bryanduxbury/roominator/photos/2012-01-26_09-58-38_41.jpg

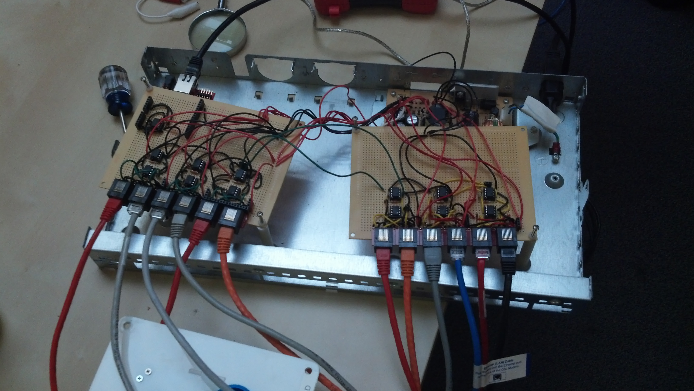
photos/2012-01-26_09-58-38_41.jpg
