bryanduxbury/roominator/photos/2012-01-26_09-58-45_927.jpg

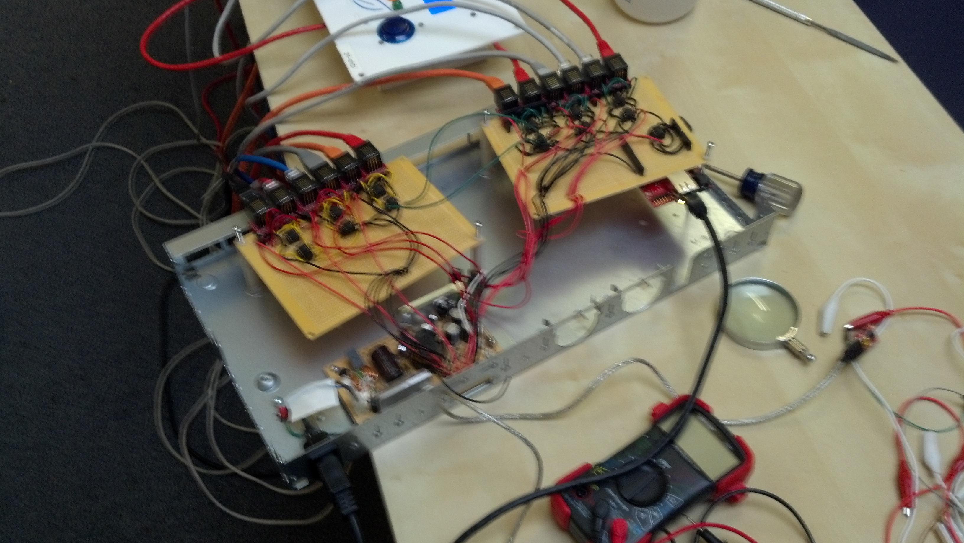
photos/2012-01-26_09-58-45_927.jpg
