bryanduxbury/roominator/photos/IMG_20111010_153513.jpg

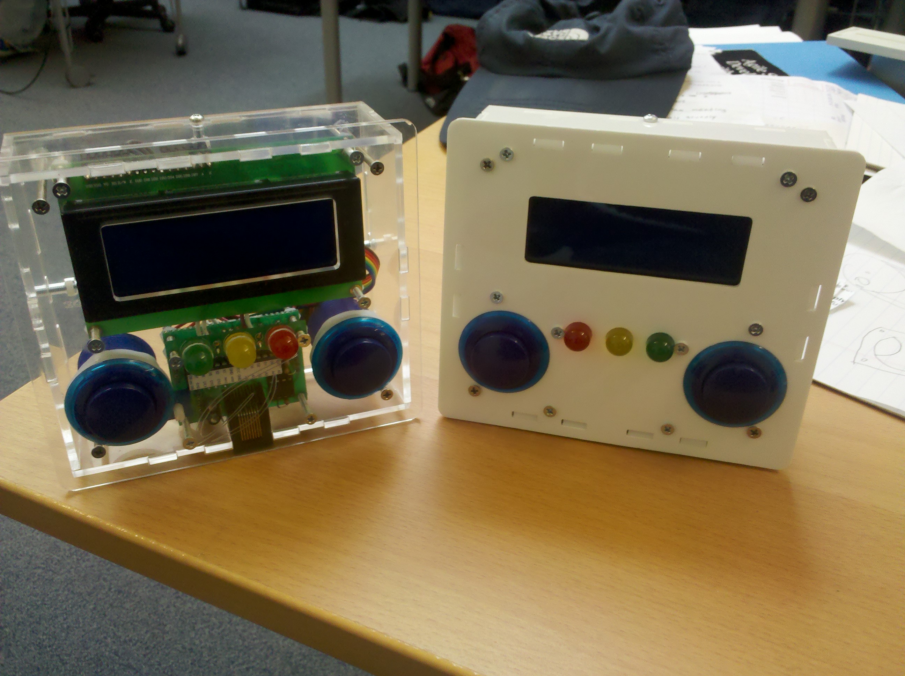
photos/IMG_20111010_153513.jpg
