bryanduxbury/roominator/source/arduino2/MasterSketch/NetworkSlave.h

#ifndef NetworkSlave_h
#define NetworkSlave_h

#include <UpstreamData.h>
#include <DownstreamData.h>

class NetworkSlave {
  public:
    NetworkSlave();
    void setDownstreamData(char*);
    void reserve();
    void cancel();
    int getReserve();
    int getCancel();
    DownstreamDataStruct* getDownstreamData();
    void clearCounts();

  private:
    UpstreamData ud;
    DownstreamData dd;

};

#endif
